cartheur/aiventure-computer/chip_2_0/catalogue/beside CPU/Beside CPU-1.png

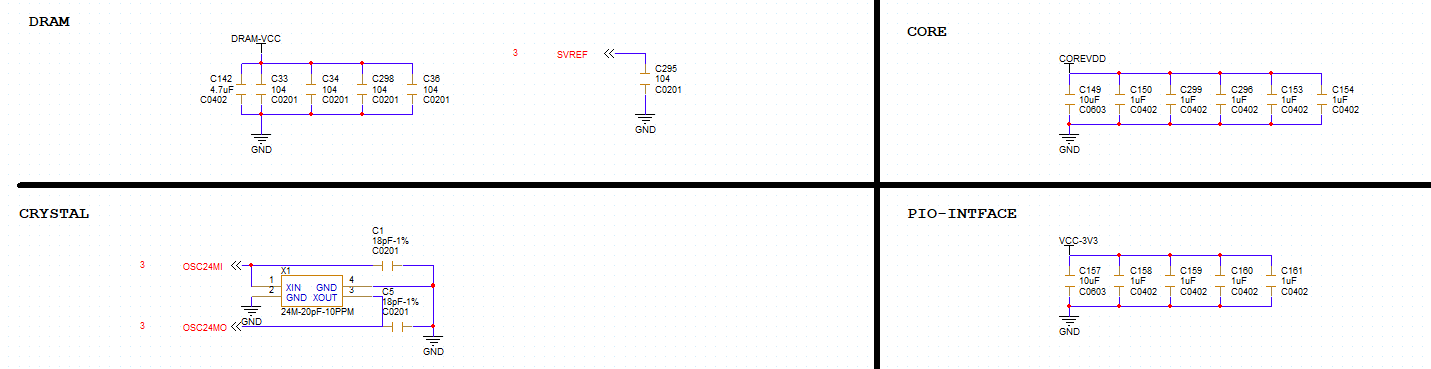
chip_2_0/catalogue/beside CPU/Beside CPU-1.png
