cartheur/aiventure-computer/chip_2_0/catalogue/beside CPU/Beside CPU.png

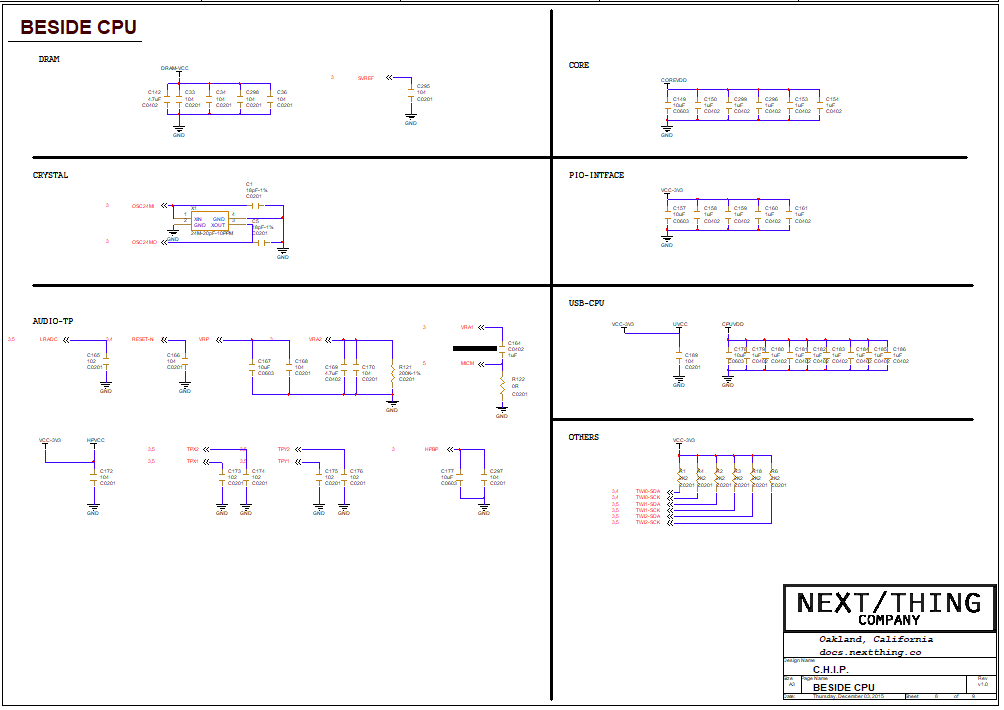
chip_2_0/catalogue/beside CPU/Beside CPU.png
