cartheur/aiventure-computer/chip_2_0/catalogue/Block/Block - 1.png

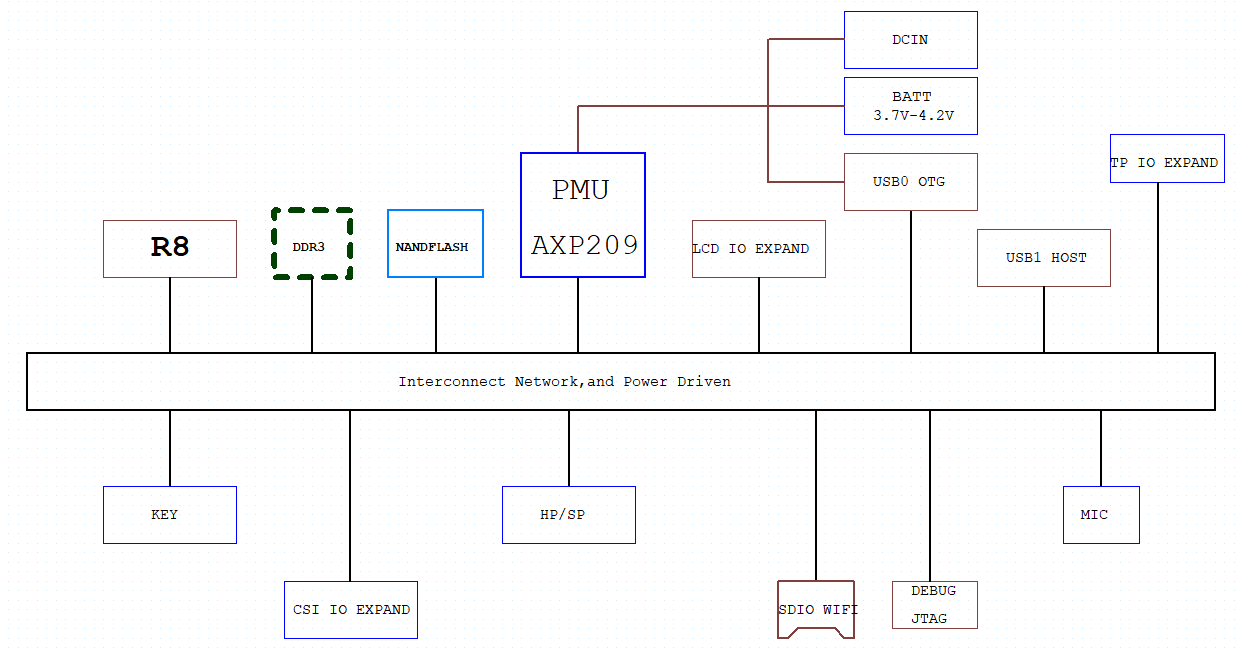
chip_2_0/catalogue/Block/Block - 1.png
