cartheur/aiventure-computer/chip_2_0/catalogue/Block/Block.png

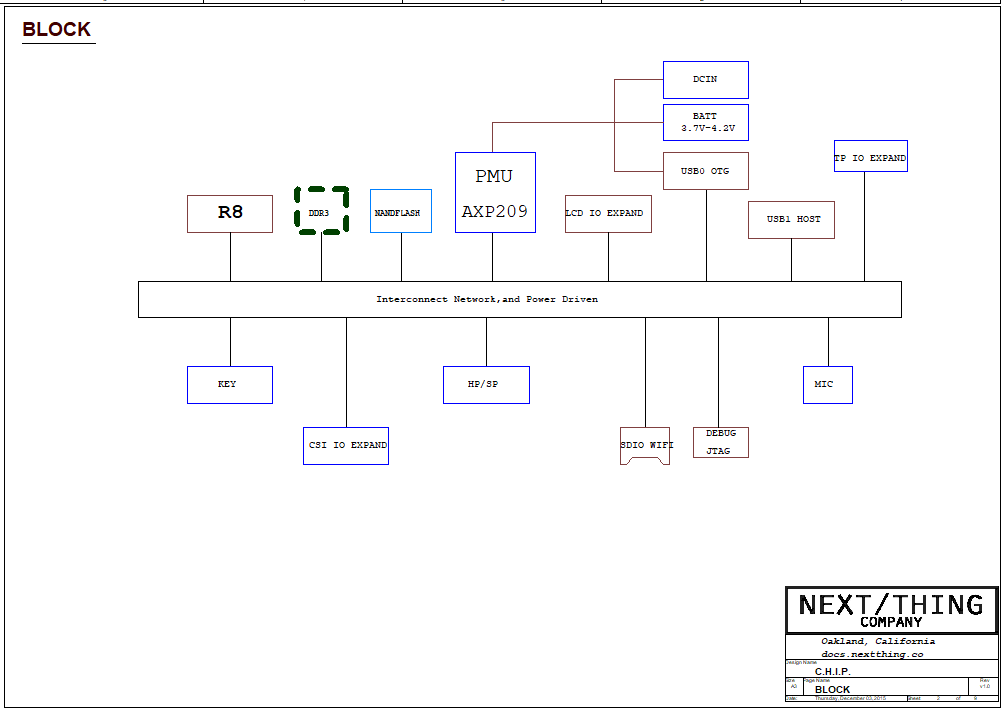
chip_2_0/catalogue/Block/Block.png
