cartheur/aiventure-computer/chip_2_0/catalogue/CPU/CPU-6.png

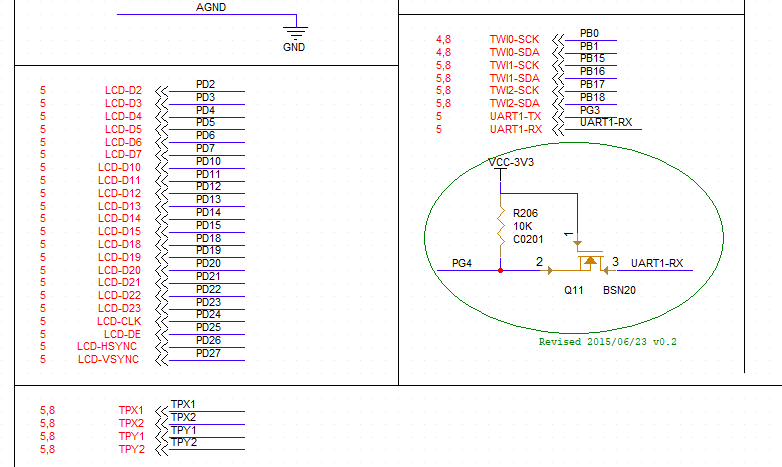
chip_2_0/catalogue/CPU/CPU-6.png
