cartheur/aiventure-computer/chip_2_0/catalogue/CPU/CPU-7.png

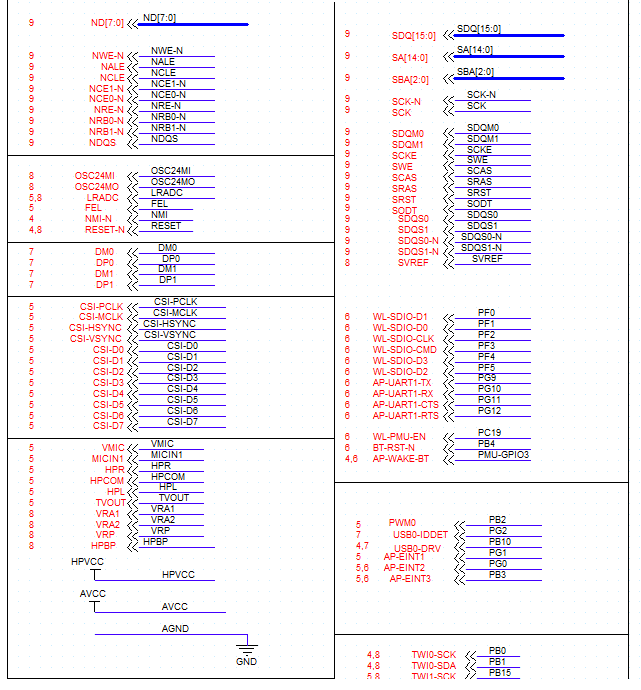
chip_2_0/catalogue/CPU/CPU-7.png
