cartheur/aiventure-computer/chip_2_0/catalogue/CPU/CPU.png

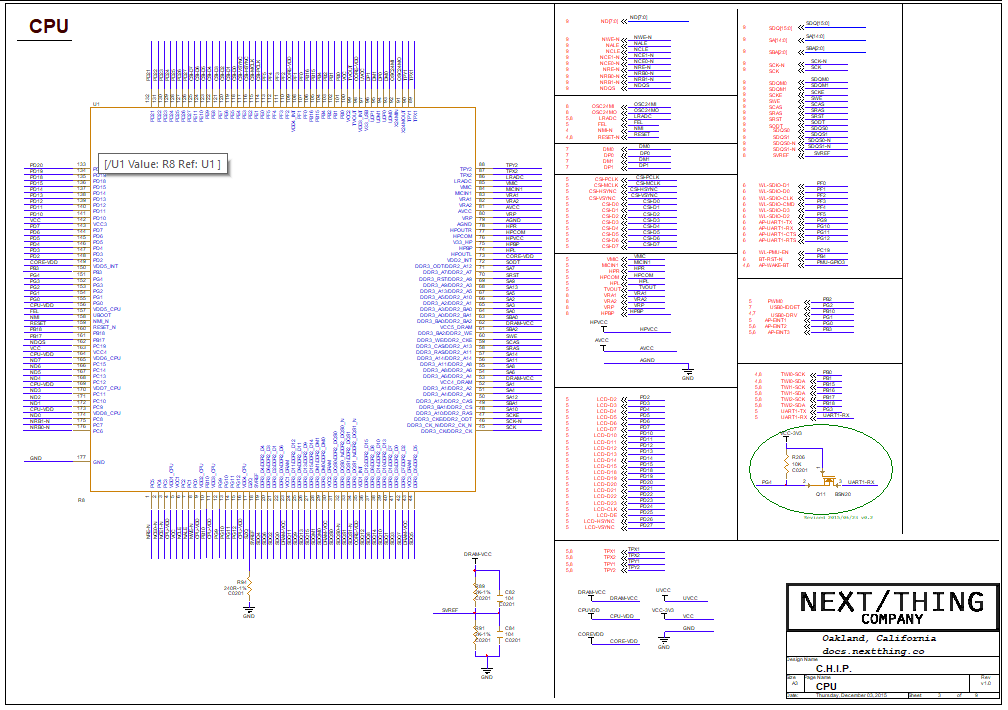
chip_2_0/catalogue/CPU/CPU.png
