cartheur/aiventure-computer/chip_2_0/catalogue/Memory/Memory-2.png

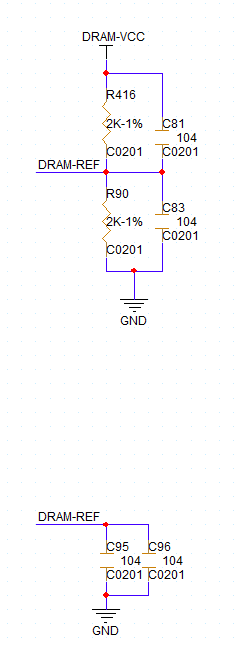
chip_2_0/catalogue/Memory/Memory-2.png
