cartheur/aiventure-computer/chip_2_0/catalogue/Memory/Memory-3.png

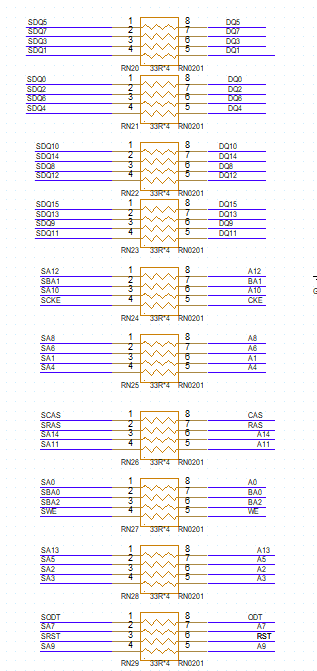
chip_2_0/catalogue/Memory/Memory-3.png
