cartheur/aiventure-computer/chip_2_0/catalogue/Memory/Memory.png

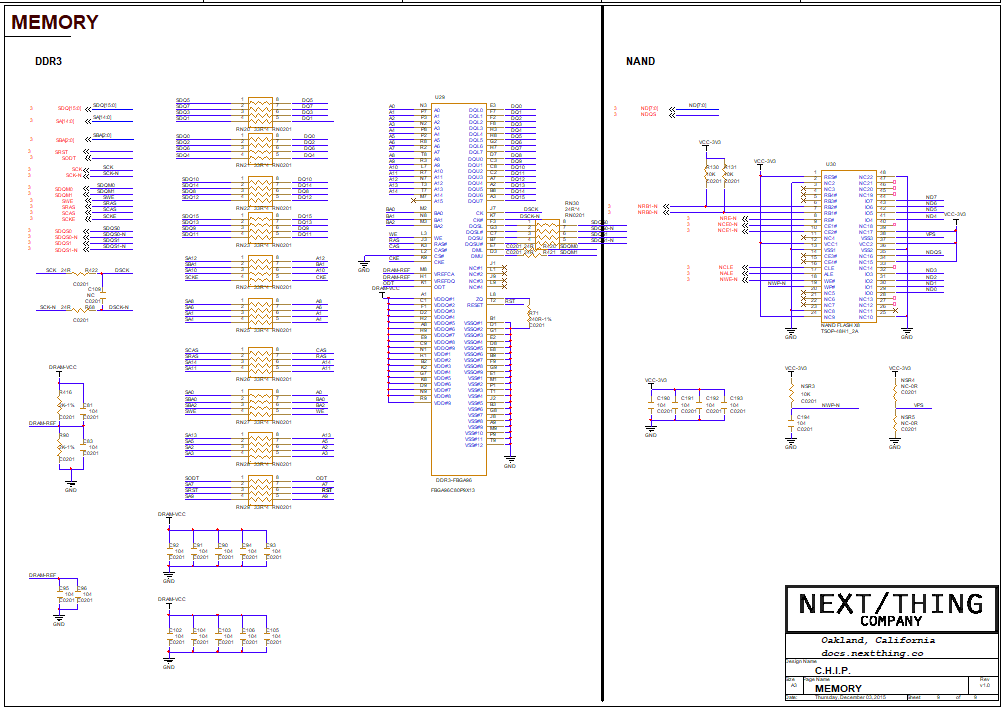
chip_2_0/catalogue/Memory/Memory.png
