cartheur/aiventure-computer/chip_2_0/catalogue/MISC/MISC-1.png

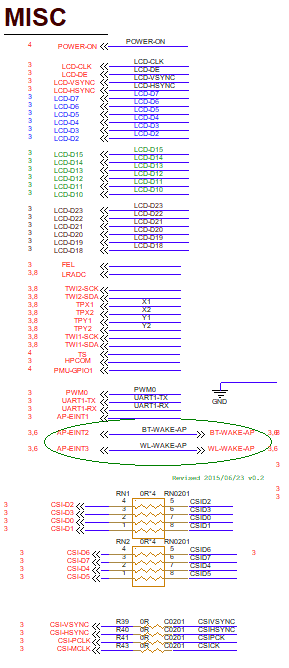
chip_2_0/catalogue/MISC/MISC-1.png
