cartheur/aiventure-computer/chip_2_0/catalogue/MISC/MISC-3.png

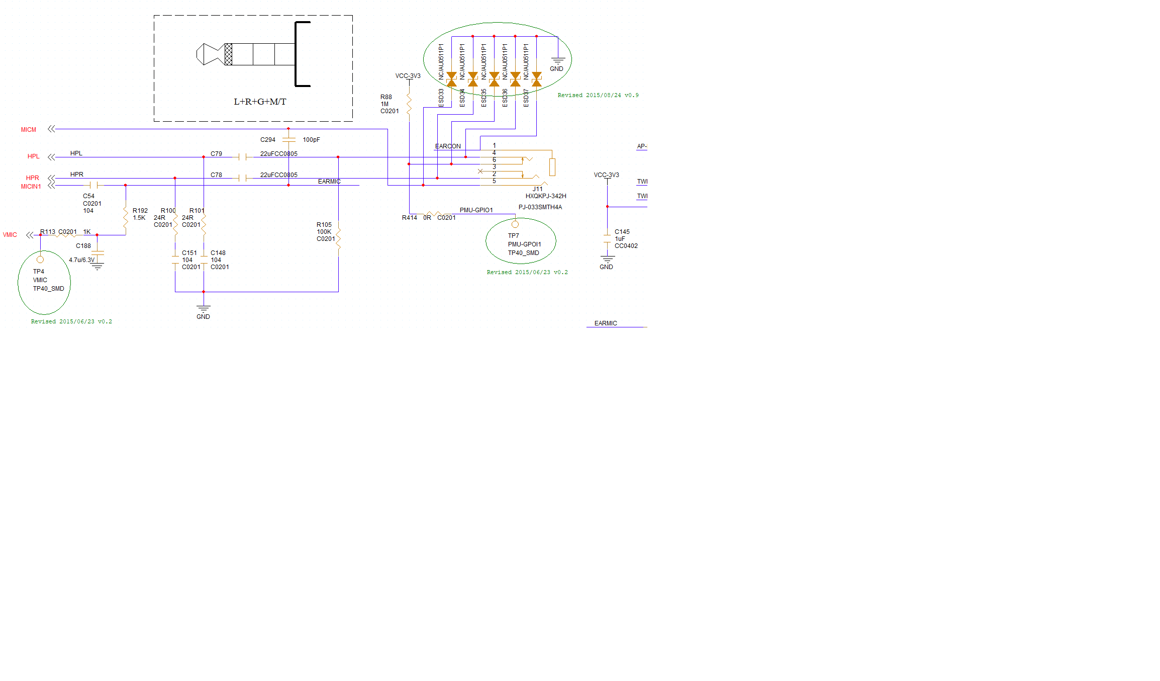
chip_2_0/catalogue/MISC/MISC-3.png
