cartheur/aiventure-computer/chip_2_0/catalogue/MISC/MISC-4.png

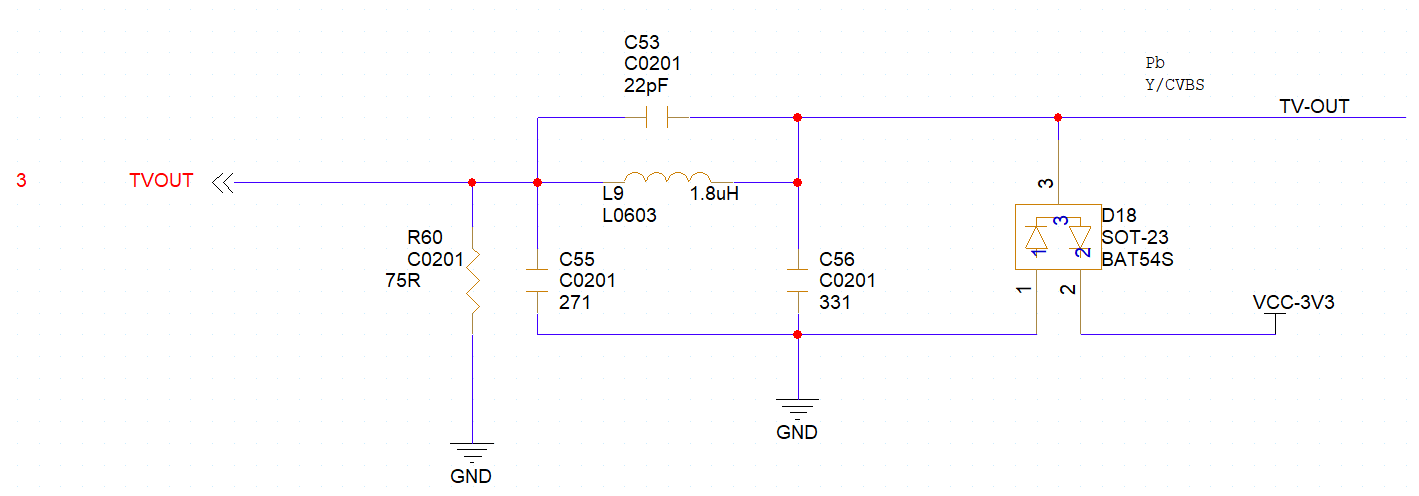
chip_2_0/catalogue/MISC/MISC-4.png
