cartheur/aiventure-computer/chip_2_0/catalogue/MISC/MISC-5.png

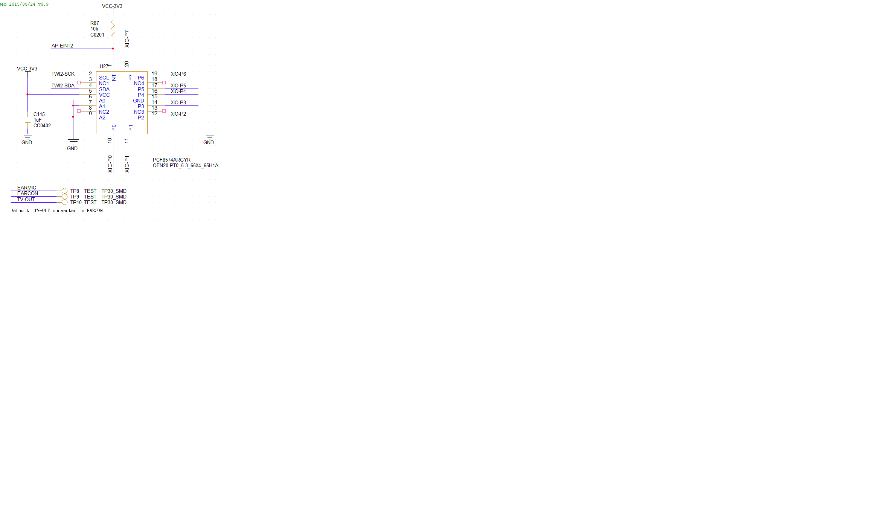
chip_2_0/catalogue/MISC/MISC-5.png
