cartheur/aiventure-computer/chip_2_0/catalogue/MISC/MISC.png

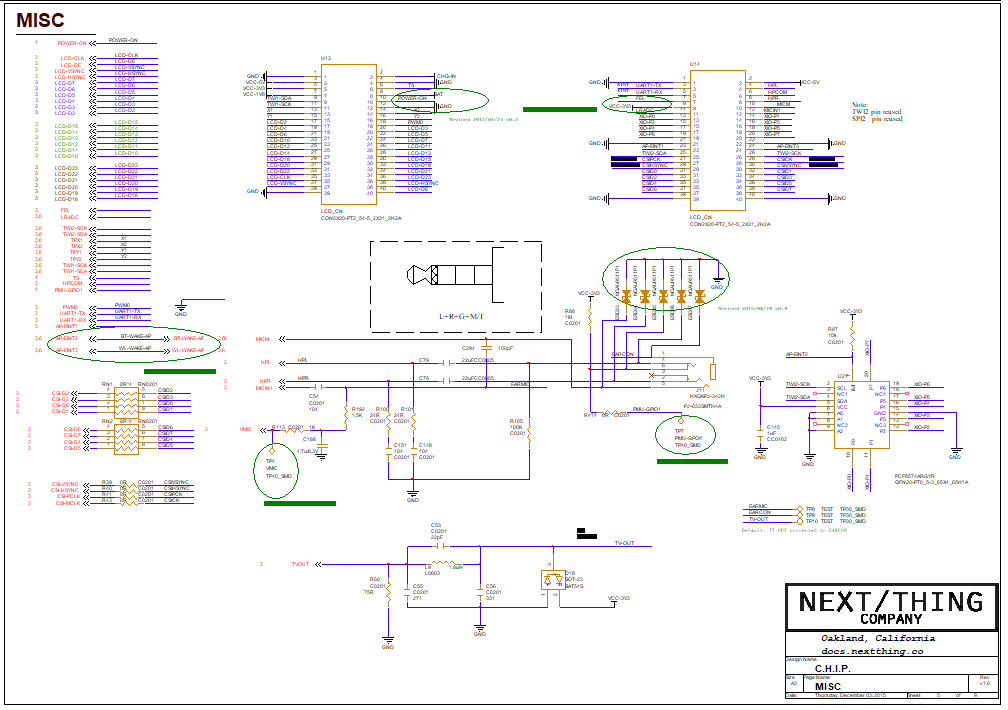
chip_2_0/catalogue/MISC/MISC.png
