cartheur/aiventure-computer/chip_2_0/catalogue/PCB/Botom layer.png

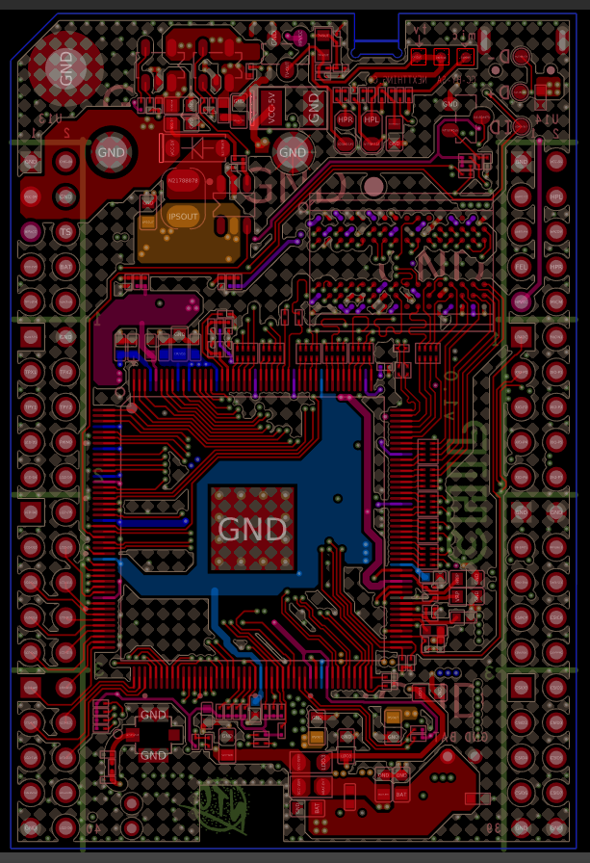
chip_2_0/catalogue/PCB/Botom layer.png
