cartheur/aiventure-computer/chip_2_0/catalogue/PCB/GND layer.png

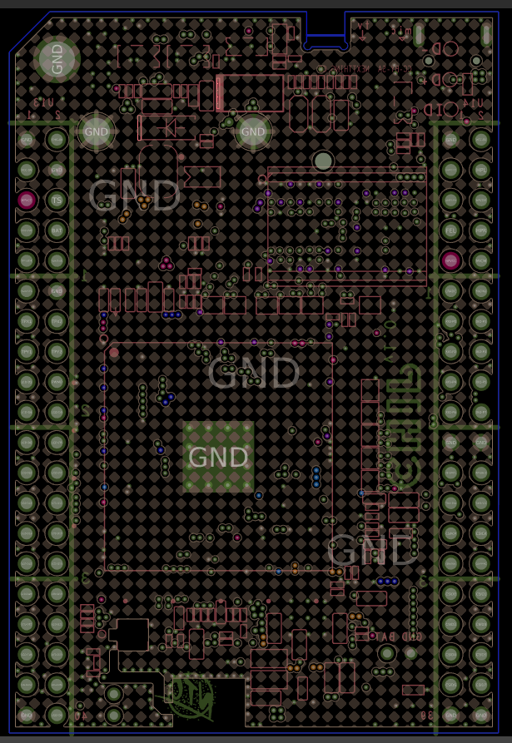
chip_2_0/catalogue/PCB/GND layer.png
