cartheur/aiventure-computer/chip_2_0/catalogue/PCB/In1 layer.png

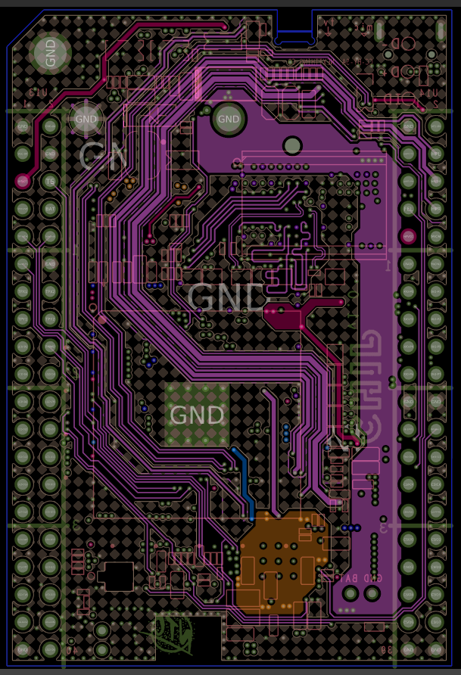
chip_2_0/catalogue/PCB/In1 layer.png
