cartheur/aiventure-computer/chip_2_0/catalogue/PCB/In2 layer.png

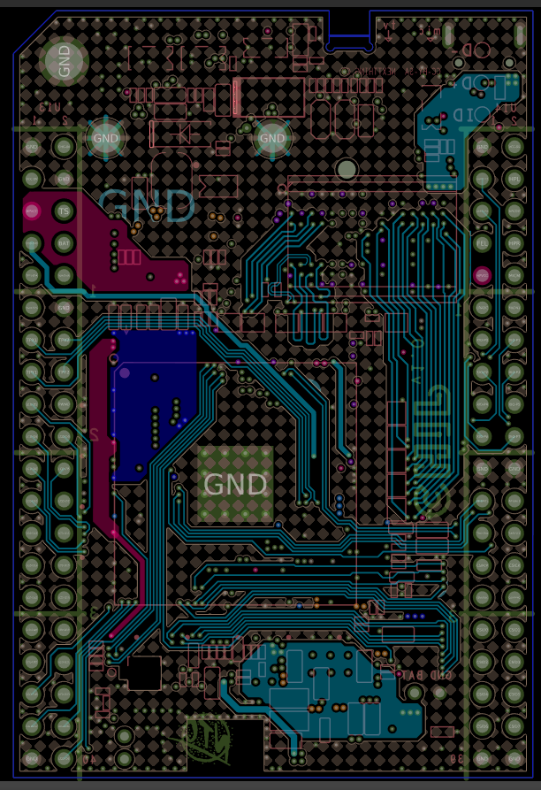
chip_2_0/catalogue/PCB/In2 layer.png
