cartheur/aiventure-computer/chip_2_0/catalogue/PCB/placement.png

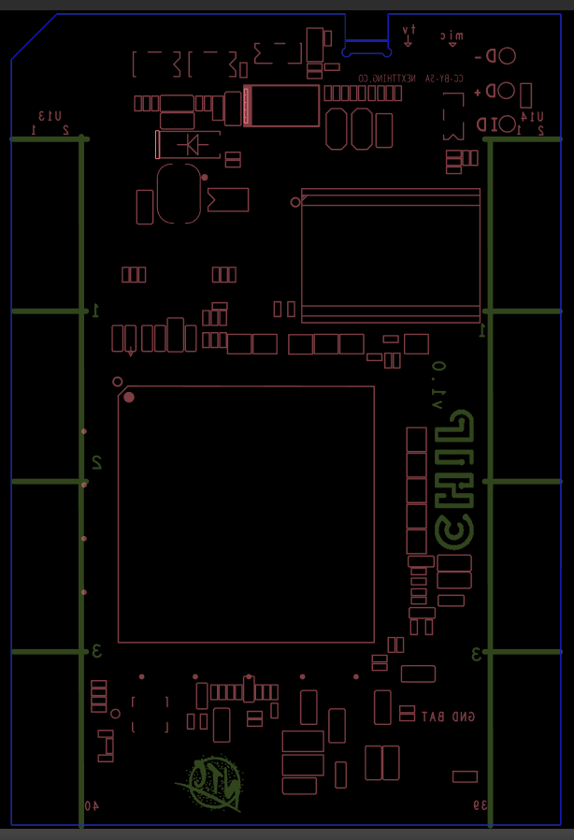
chip_2_0/catalogue/PCB/placement.png
