cartheur/aiventure-computer/chip_2_0/catalogue/PCB/TOP layer.png

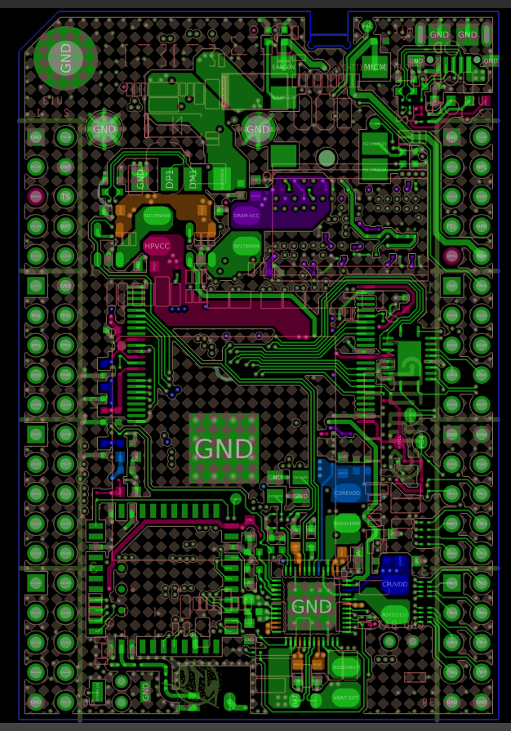
chip_2_0/catalogue/PCB/TOP layer.png
