cartheur/aiventure-computer/chip_2_0/catalogue/power/power-1.png

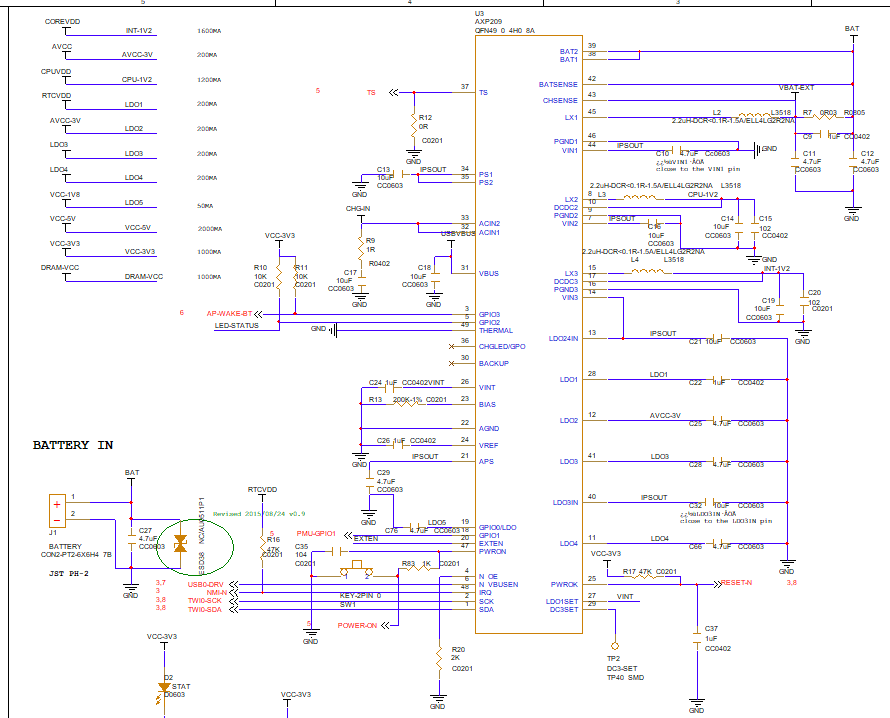
chip_2_0/catalogue/power/power-1.png
