cartheur/aiventure-computer/chip_2_0/catalogue/power/power-2.png

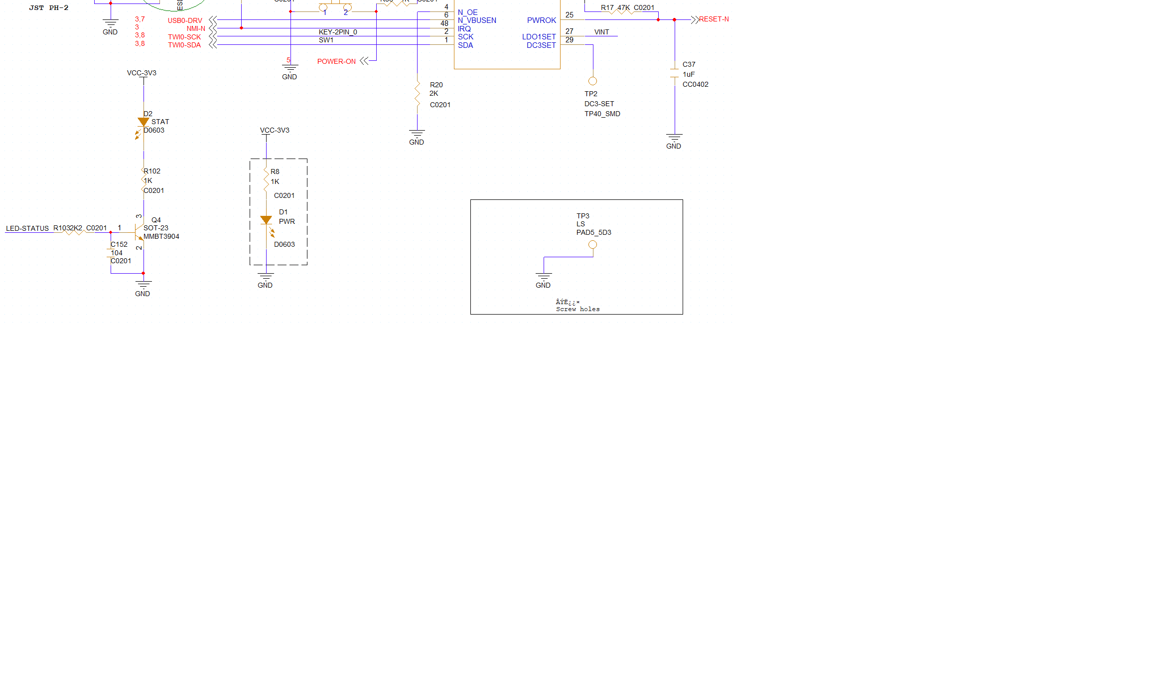
chip_2_0/catalogue/power/power-2.png
