cartheur/aiventure-computer/chip_2_0/catalogue/power/power.png

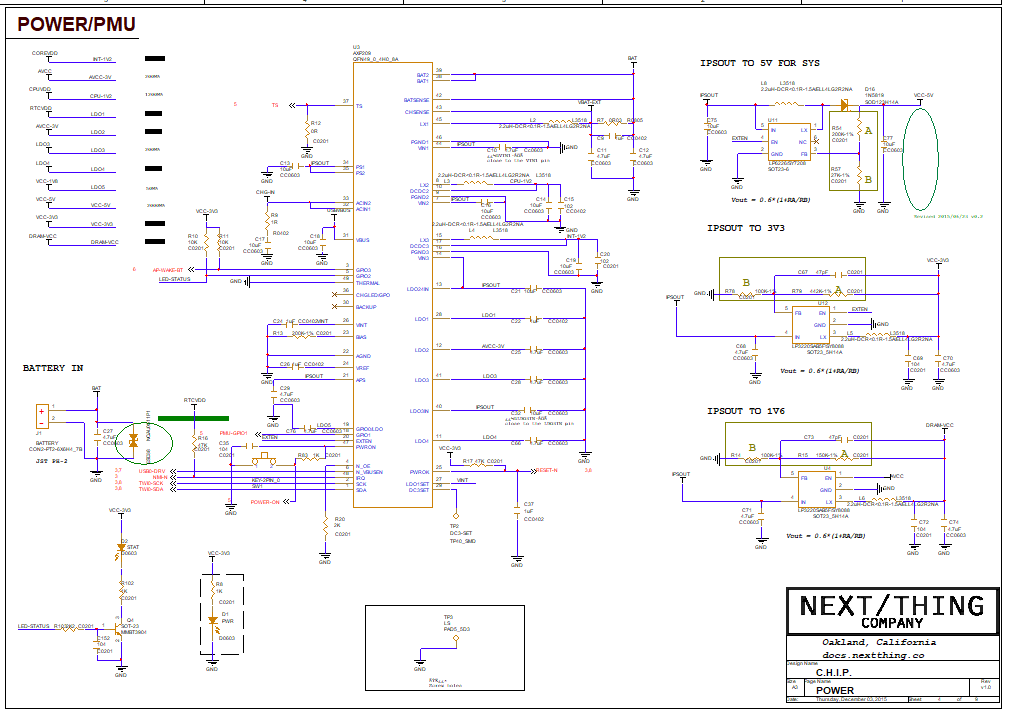
chip_2_0/catalogue/power/power.png
