cartheur/aiventure-computer/chip_2_0/catalogue/USB/USB-1.png

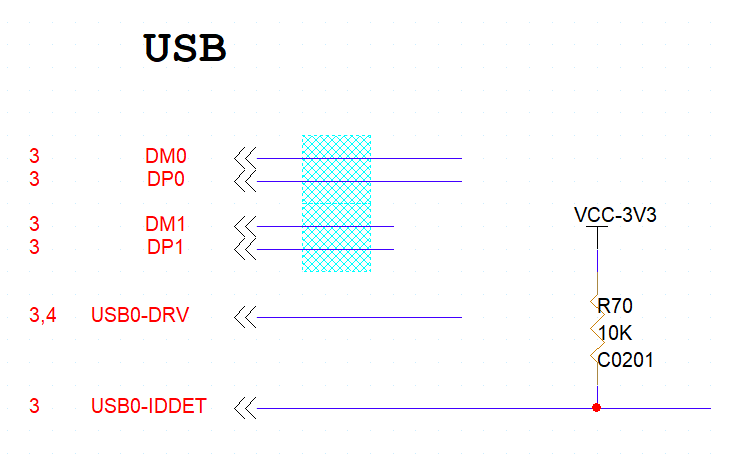
chip_2_0/catalogue/USB/USB-1.png
