cartheur/aiventure-computer/chip_2_0/catalogue/USB/USB-2.png

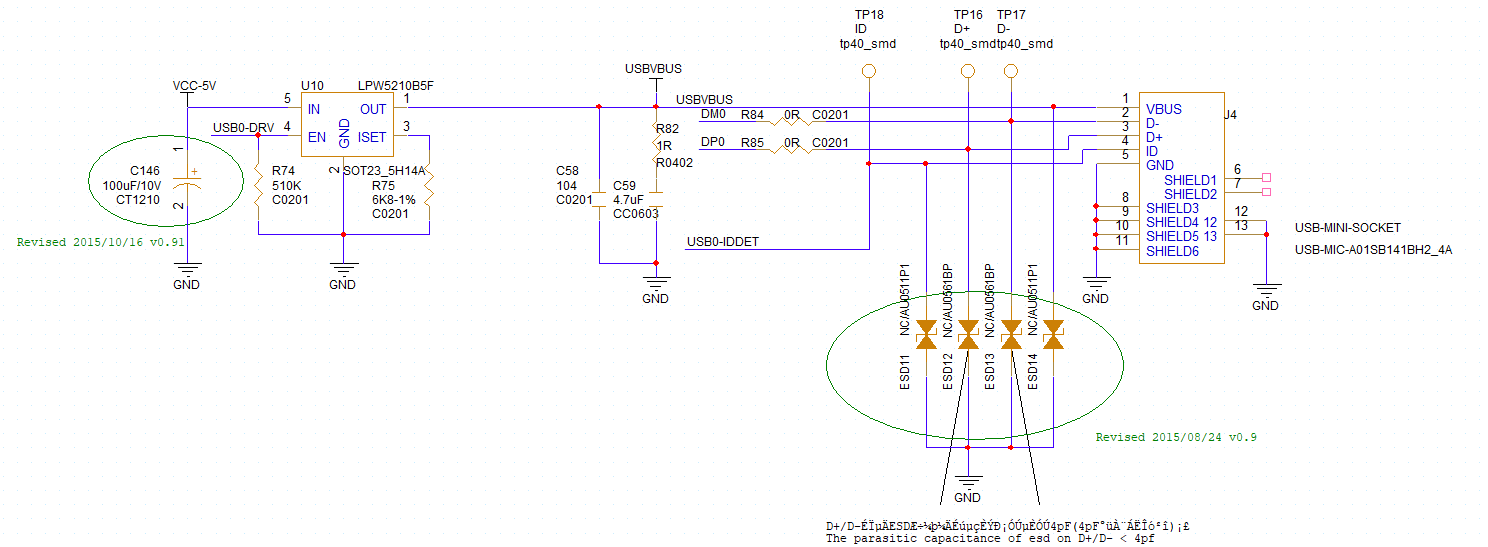
chip_2_0/catalogue/USB/USB-2.png
