cartheur/aiventure-computer/chip_2_0/catalogue/USB/USB.png

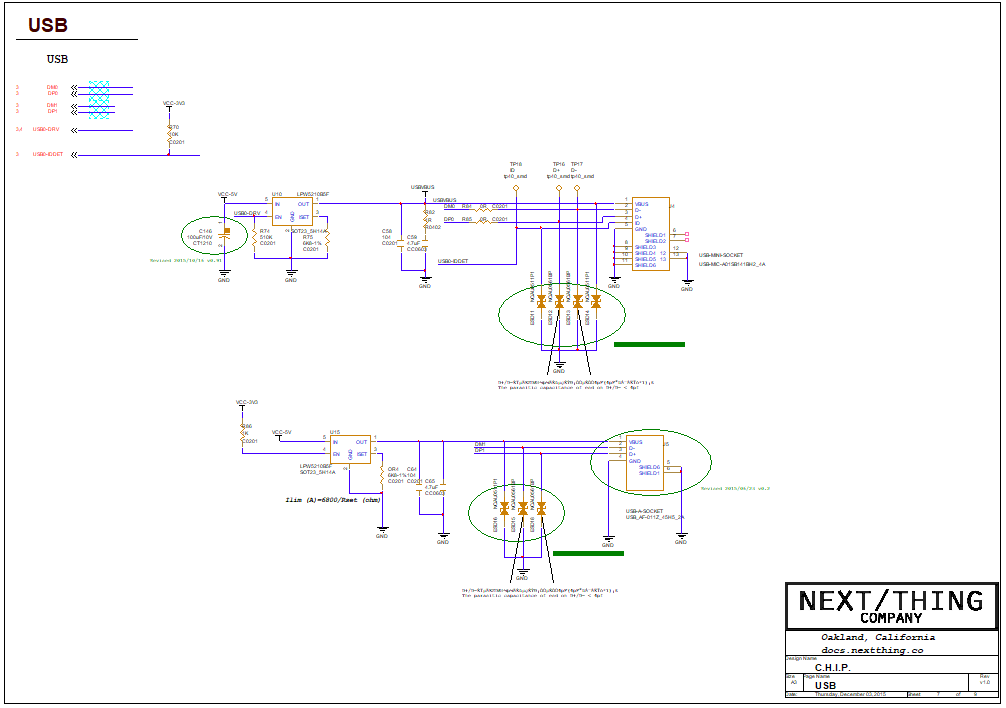
chip_2_0/catalogue/USB/USB.png
