cartheur/aiventure-computer/chip_2_0/catalogue/WiFi and BT/WiFi-BT-1.png

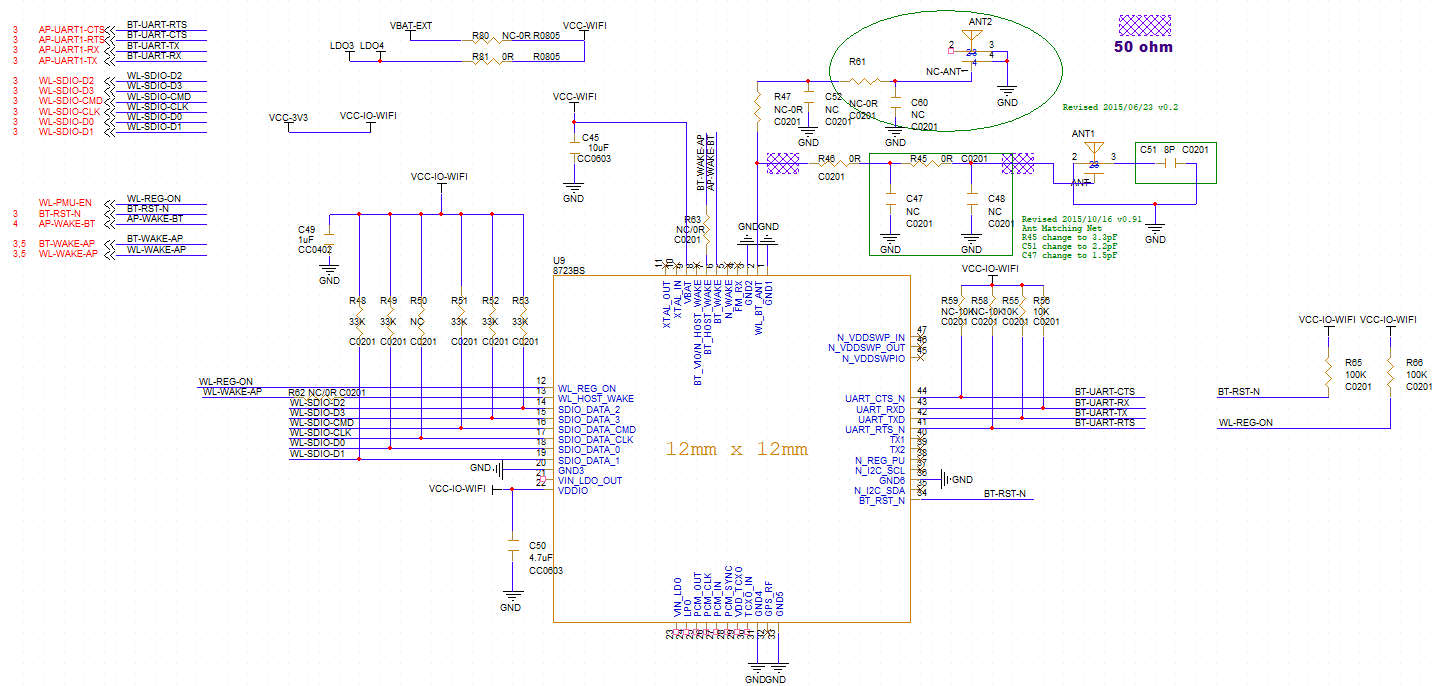
chip_2_0/catalogue/WiFi and BT/WiFi-BT-1.png
