cartheur/aiventure-computer/chip_2_0/catalogue/WiFi and BT/WiFi-BT.png

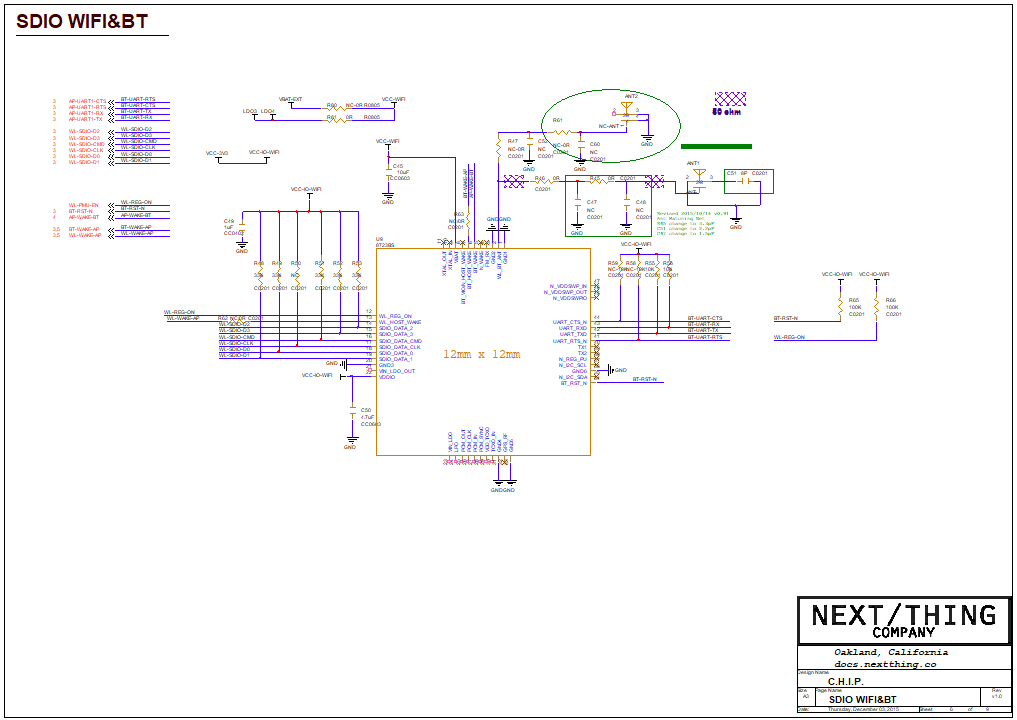
chip_2_0/catalogue/WiFi and BT/WiFi-BT.png
