cartheur/aiventure-computer/chip_2_0/catalogue/Revision History/Revision History - 1.png

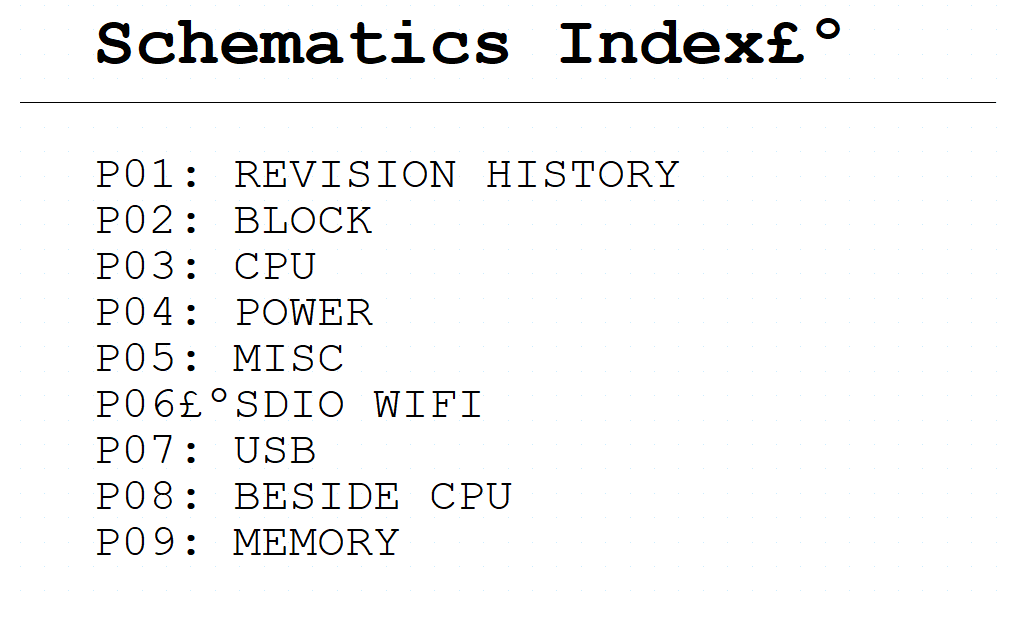
chip_2_0/catalogue/Revision History/Revision History - 1.png
