cartheur/aiventure-computer/chip_2_0/catalogue/Revision History/Revision History - 2.png

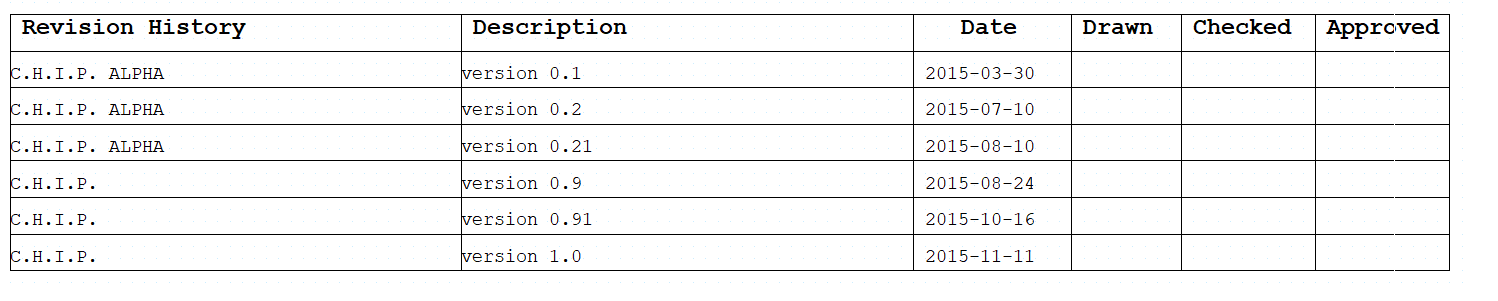
chip_2_0/catalogue/Revision History/Revision History - 2.png
