cartheur/aiventure-computer/chip_2_0/project/first/03 CPU-SchDoc.sch

## KiCad design chip_2_0/project/first/03 CPU-SchDoc.sch (2024-04-20)

Schematic: 03 CPU-SchDoc.sch

Parts:
*_3: (no value)
IC3: R8
IC4: 10K
IC5, IC9: 2K-1%
IC6: BSN20
IC7, IC10: 104
IC8: 240R-1%

Notes on the sheet:
C.H.I.P.~
v1.0
CPU
March~~8,~1995
DRAM
Revised 2015/06/23 v0.2
