cartheur/aiventure-computer/chip_2_0/project/first/04 POWER-SchDoc.sch

## KiCad design chip_2_0/project/first/04 POWER-SchDoc.sch (2024-04-20)

Schematic: 04 POWER-SchDoc.sch

Parts:
*_4: (no value)
IC12: 150K-1%
IC13: PWR
IC14, IC26, IC28, IC33, IC36, IC41, IC48, IC60, IC79, IC85: 10uF
IC15: DC3-SET
IC16, IC23, IC27, IC30, IC31, IC32, IC34, IC35, IC38, IC40, IC50, IC54, IC67: 4.7uF
IC17, IC20, IC42, IC57, IC72, IC78: 2.2uH-DCR<0.1R-1.5A/ELL4LG2R2NA
IC18, IC47, IC58, IC70, IC73: 1uF
IC19, IC52, IC65, IC71: 104
IC21, IC75: 100K-1%
IC22: LP3220SAB5F\SY8088
IC24, IC84: 102
IC25: 2K2
IC29, IC46: 10K
IC37: 442K-1%
IC39: 1R
IC43, IC74: 47K
IC44: NC/AU0511P1
IC45: LS
IC49: 0R
IC51, IC69, IC80: 1K
IC53, IC56: 200K-1%
IC55, IC66: 47pF
IC59: KEY-2PIN_0
IC61: MMBT3904
IC62: LP3220SAB5F/SY8088
IC63: 0R03
IC64: 27K-1%
IC68: LP6226/SY7208
IC76: BATTeRY
IC77: 1N5819
IC81: AXP209
IC82: STAT
IC83: 2K

Notes on the sheet:
C.H.I.P.~
v1.0
POWER
March~~8,~1995
WILL~ESD9B5V~Bidirection~ESD~Protection
MODEM
POWER/PMU
BATTERY IN
IPSOUT TO 5V FOR SYS
IPSOUT TO 3V3
IPSOUT TO 1V6
Vout = 0.6*(1+RA/RB)
200MA
2000MA
JST PH-2
Revised 2015/06/23 v0.2
1600MA
1200MA
50MA
1000MA
Revised 2015/08/24 v0.9
