cartheur/aiventure-computer/chip_2_0/project/first/05 MISC-SchDoc.sch

## KiCad design chip_2_0/project/first/05 MISC-SchDoc.sch (2024-04-20)

Schematic: 05 MISC-SchDoc.sch

Parts:
*_5: (no value)
IC87, IC88: LCD_CN
IC89, IC113: 24R
IC90, IC100: 0R*4
IC91, IC99, IC112, IC123, IC125: NC/AU0511P1
IC92, IC104: 22uF
IC93, IC111, IC120: 104
IC94, IC102, IC114, IC118, IC128: 0R
IC95: 10K
IC96, IC98, IC121: TEST
IC97: 100pF
IC101: 1.5K
IC103: VMIC
IC105: BAT54S
IC106: 4.7u/6.3V
IC107: 75R
IC108: 1.8uH
IC109: 271
IC110: 1uF
IC115: PCF8574ARGYR
IC116: 100K
IC117: HXQKPJ-342H
IC119: PMU-GPOI1
IC122: 1K
IC124: 1M
IC126: 331
IC127: 22pF

Notes on the sheet:
C.H.I.P.~
v1.0
MISC
March~~8,~1995
GRM1555C1H180JZ01
MURATA/YIXING
GRM1555C1H101JZ01/C0402CG101J050AT
C0100019A/C0100019D
WILL~ESD9B5V~Bidirection~ESD~Protection
C0200004A/C0200004C/C0200004D
YIXING/MURATA/YIXING
C0603B225K006AT/GRM185R60J225KE26/C0603B225M006AT
EJ225K6V3631
TVLCD
Y/CVBS
L+R+G+M/T
SPI2_MOSI
SPI2_CS0
SPI2_MISO
SPI2_CLK
EINT
Revised 2015/06/23 v0.2
Revised 2015/08/24 v0.9
Default: TV-OUT connected to EARCON
Revised 2015/10/16 v0.91
