cartheur/aiventure-computer/chip_2_0/project/first/06 SDIO WIFI&BT-SchDoc.sch

## KiCad design chip_2_0/project/first/06 SDIO WIFI&BT-SchDoc.sch (2024-04-20)

Schematic: 06 SDIO WIFI&BT-SchDoc.sch

Parts:
*_6: (no value)
IC130: 8P
IC131, IC144: 10K
IC132: NC-ANT
IC133, IC143, IC152: NC-0R
IC134, IC136, IC155: 0R
IC135, IC145: 100K
IC137, IC138, IC140, IC151, IC154: 33K
IC139, IC148: NC/0R
IC141, IC146, IC157, IC158, IC159: NC
IC142: ANT
IC147: 4.7uF
IC149: 8723BS
IC150: 10uF
IC153, IC156: NC-10K
IC160: 1uF

Notes on the sheet:
C.H.I.P.~
v1.0
SDIO~WIFI&BT
March~~8,~1995
AMPAK_SIP
AMPAK
MODULE
SDIO WIFI&BT
50 ohm
Revised 2015/06/23 v0.2
