cartheur/aiventure-computer/chip_2_0/project/first/07 USB-SchDoc.sch

## KiCad design chip_2_0/project/first/07 USB-SchDoc.sch (2024-04-20)

Schematic: 07 USB-SchDoc.sch

Parts:
*_7: (no value)
IC162: D+
IC163, IC165, IC171: NC/AU0511P1
IC164, IC173, IC179, IC187: NC/AU0561BP
IC166: USB-A-SOCKET
IC167, IC174: 0R
IC168, IC169: 104
IC170: 10K
IC172: D-
IC175: 510K
IC176, IC178: 4.7uF
IC177: ID
IC180, IC188: LPW5210B5F
IC181: 1K
IC182: 100uF/10V
IC183, IC186: 6K8-1%
IC184: USB-MINI-SOCKET
IC185: 1R

Notes on the sheet:
C.H.I.P.~
v1.0
USB
March~~8,~1995
MODEM
WILL~ESD9B5V~Bidirection~ESD~Protection
Ilim (A)=6800/Rset (ohm)
Revised 2015/06/23 v0.2
Revised 2015/08/24 v0.9
Revised 2015/10/16 v0.91
