cartheur/aiventure-computer/chip_2_0/project/first/08 BESIDE CPU-SchDoc.sch

## KiCad design chip_2_0/project/first/08 BESIDE CPU-SchDoc.sch (2024-04-20)

Schematic: 08 BESIDE CPU-SchDoc.sch

Parts:
*_8: (no value)
IC190, IC194, IC198, IC199, IC204, IC206, IC208, IC212, IC213, IC217, IC224, IC227, IC229, IC230, IC235, IC238, IC239, IC240: 1uF
IC191, IC196, IC200, IC201, IC203, IC205, IC209, IC215, IC218, IC222, IC223: 104
IC192, IC202, IC210, IC220, IC226, IC234: 2K2
IC193: 0R
IC195, IC214, IC216, IC228, IC231: 10uF
IC197: 200K-1%
IC207, IC219, IC221, IC232, IC237: 102
IC211, IC241: 18pF-1%
IC225, IC236: 4.7uF
IC233: 24M-20pF-10PPM

Notes on the sheet:
C.H.I.P.~
v1.0
BESIDE~CPU
March~~8,~1995
TXC
7M24000004
U3000019A
AUDIO-TP
DRAM
PIO-INTFACE
OTHERS
USB-CPU
CORE
BESIDE CPU
µçÈÝÖµ²»¿É¸ü¸Ä
CRYSTAL
