cartheur/aiventure-computer/chip_2_0/project/first/09 DDR3-SchDoc.sch

## KiCad design chip_2_0/project/first/09 DDR3-SchDoc.sch (2024-04-20)

Schematic: 09 DDR3-SchDoc.sch

Parts:
*_9: (no value)
IC243, IC247, IC268, IC275: 24R
IC244, IC251, IC253, IC254, IC256, IC257, IC261, IC262, IC265, IC270, IC271, IC272, IC273, IC274, IC276, IC279, IC281, IC283, IC287: 104
IC245, IC249, IC269: 10K
IC246: 24R*4
IC248, IC250, IC252, IC255, IC258, IC260, IC266, IC284, IC285, IC286: 33R*4
IC259, IC278: NC-0R
IC263, IC280: 2K-1%
IC264: NAND FLASH X8
IC267: DDR3-FBGA96
IC277: 240R-1%
IC282: NC

Notes on the sheet:
C.H.I.P.~
v1.0
MEMORY
March~~8,~1995
DDR3
NAND
